maelastiques/PTCR/components-models/E22-900M22S.step

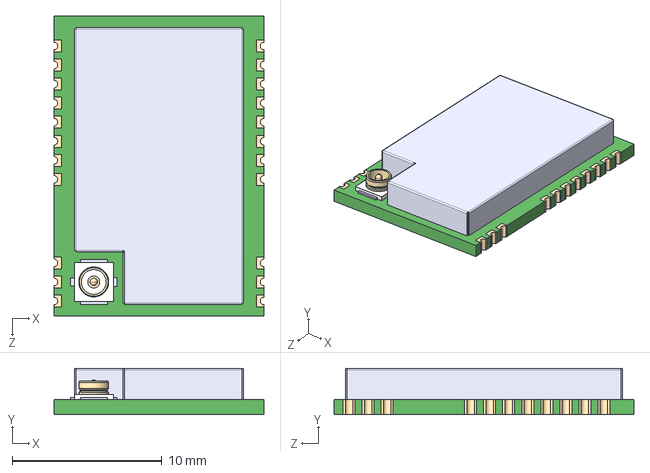
[picture p22: CAD file, 2026-03-16]
components-models/E22-900M22S.step
14.0 x 3.10 x 20.0 mm
