maelastiques/PTCR/components-models/L86-M33.stp

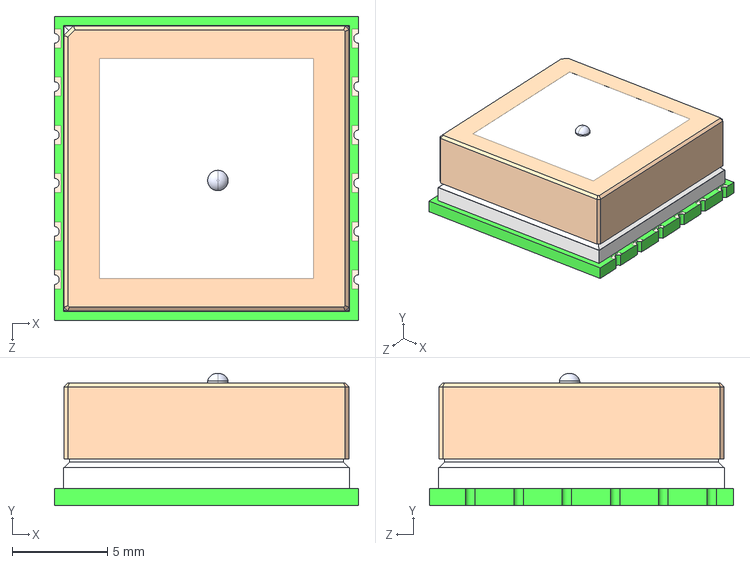
[picture p23: CAD file, 2026-03-16]
components-models/L86-M33.stp
16.0 x 6.95 x 16.0 mm
