maelastiques/PTCR/components-models/TPS62842DGRR.stp

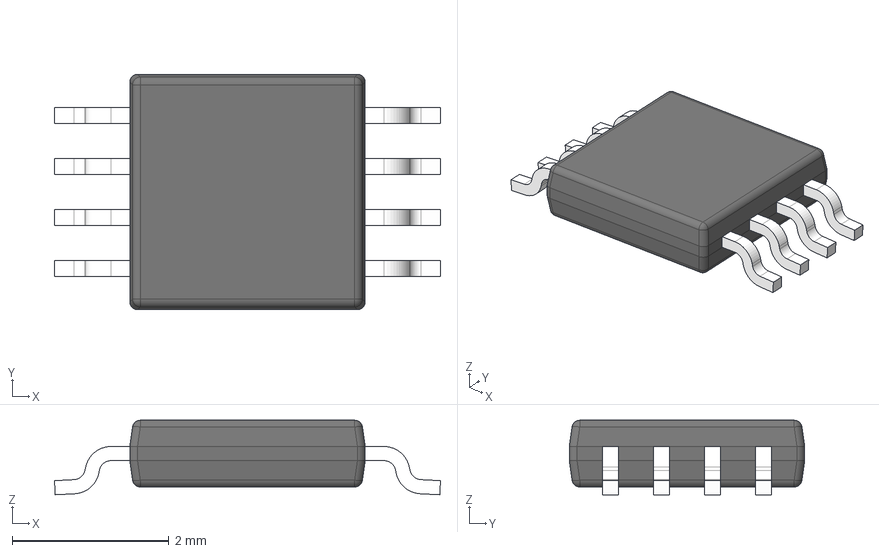
[picture p24: CAD file, 2026-03-16]
components-models/TPS62842DGRR.stp
4.92 x 3.00 x 0.95 mm
BODY-SO
LEAD-SO x 8
THERMALPAD-SO
