maelastiques/PTCR/components-models/MCP23017-E_SO.stp

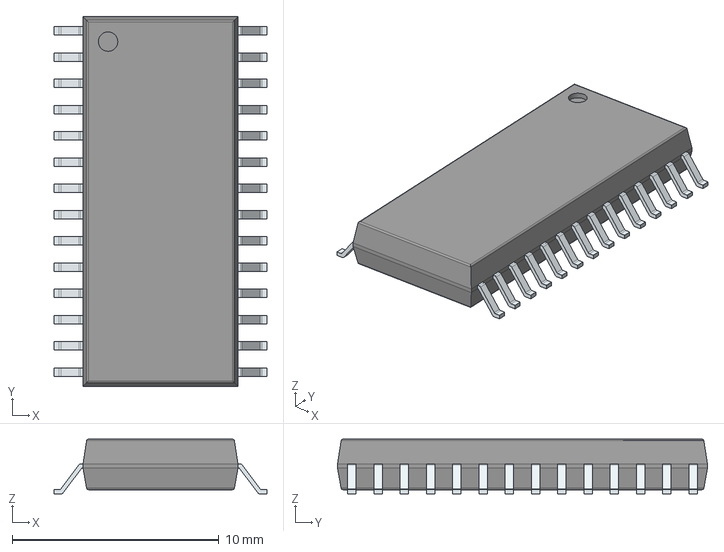
[picture p25: CAD file, 2026-03-16]
components-models/MCP23017-E_SO.stp
10.3 x 17.9 x 2.65 mm
PinsArrayLR
